fake-name/EORE/Code/Prototypes/SWR Sweeper/takeSweeps.py

import time

import eore
import SignalHound as sh
import logSetup



ACQ_SPAN               = 27e6
ACQ_REF_LEVEL_DB       = -20
ACQ_ATTENUATION_DB     = 20
ACQ_GAIN_SETTING       = 0
ACQ_RBW                = 2.465e3
ACQ_VBW                = ACQ_RBW
ACQ_SWEEP_TIME_SECONDS = 0.0100
ACQ_WINDOW_TYPE        = "hamming"
ACQ_UNITS              = "power"
ACQ_TYPE               = "sweeping"
ACQ_MODE               = "average"
ACQ_Y_SCALE            = "log-scale"

# The offset from center to locate the sampling bin at.
SAMPLE_OFFSET          = 5e6

class SweeperSignalHound(sh.SignalHound):


	def setupSignalhound(self, freq=100e6):
		self.configureAcquisition(ACQ_MODE, ACQ_Y_SCALE)
		self.configureCenterSpan(center = freq+5e6, span = ACQ_SPAN)
		self.configureLevel(ref = ACQ_REF_LEVEL_DB, atten = ACQ_ATTENUATION_DB)
		self.configureGain(gain = ACQ_GAIN_SETTING)
		self.configureSweepCoupling(rbw = ACQ_RBW, vbw = ACQ_VBW, sweepTime = ACQ_SWEEP_TIME_SECONDS, rbwType = "native", rejection = "no-spur-reject")
		self.configureWindow(window = ACQ_WINDOW_TYPE)
		self.configureProcUnits(units = ACQ_UNITS)
		self.configureTrigger(trigType = "none", edge = "rising-edge", level = 0, timeout = 5)
		# self.configureIO("dc", "int-ref-out", "out-logic-low")
		# self.configureDemod("fm", 102.3e6, 250e3, 12e3, 20, 50)

		# self.configureRawSweep(100, 8, 2)
		self.initiate(mode = ACQ_TYPE, flag = "ignored")
		print(self.getCurrentAcquisitionSettings())

	def setAcqCenterFreq(self, freq):
		self.configureCenterSpan(center = freq, span = ACQ_SPAN)
		self.initiate(mode = ACQ_TYPE, flag = "ignored")

	def getPowerAtFreq(self, freq):

		self.setAcqCenterFreq(freq-SAMPLE_OFFSET)

		trace = self.fetchTrace()
		traceSize = len(trace['max'])
		# Binsize is span divided by number of returned points
		acqBinSize = ACQ_SPAN / traceSize

		# the offset of the frequency we're interested in is
		binFreqOffset = int(SAMPLE_OFFSET / acqBinSize)

		binFreqCenter = (traceSize / 2) + binFreqOffset

		# Return the max of the three frequency bins around the point of interest
		ret = max(trace['max'][binFreqCenter-3:binFreqCenter+4])

		# print(traceSize, trace['max'].argmax(), binFreqCenter)
		print(ret, max(trace['max']))
		# print(trace['max'][binFreqCenter-1:binFreqCenter+4])

		return ret

def frange(x, y, jump):
	while x <= y:
		yield x
		x += jump


# import matplotlib
# matplotlib.use("WxAgg")		#Change ploting backend

import matplotlib.pyplot as pplt
import numpy as np

def plot(dataset):
	mainWin = pplt.figure()

	plot1 = mainWin.add_subplot(1,1,1)			#And plot them

	x = []
	y = []
	for xVal, yVal in dataset:
		if y < -60:
			continue
		if x < -60:
			continue

		x.append(xVal)
		y.append(yVal)

	plot1.plot(x, y)

	pplt.show()

def go():
	print("Starting")
	# logSetup.initLogging()
	print("Loggers initialized")
	# port = EoreController("COM4")
	port = eore.EoreController("COM40")
	print("Port opened")

	x = 0
	port.writeAtten(eore.MAIN_TONE_ATTEN,       20)
	port.writeAtten(eore.SWITCH_SWR_TONE_ATTEN, 10)
	port.writeAtten(eore.NOISE_DIODE_ATTEN,     0)
	port.writeAtten(eore.AUX_TONE_ATTEN,        0)
	port.writeAtten(eore.SWITCH_TONE_ATTEN,     0)
	port.writeAtten(eore.MID_AMP_ATTEN,         10)


	port.writeSwitch(eore.MAIN_SW, eore.SW_MAIN_INPUT)
	port.writeSwitch(eore.TONE_SW, eore.SW_TONE_SWR_COUPLER)

	# port.writeAtten(2, 31.5)

	port.writeOscillator(0, 100e6)

	START = 100e6
	STOP  = 200e6

	# START = 195.0e6
	# STOP  = 200.0e6
	STEP  = 2.5e5


	# while (1):
	# return

	hound = SweeperSignalHound()
	print("SignalHound connected")
	hound.setupSignalhound()
	print("SignalHound configured")


	data = []

	with open("log - %s.csv" % time.time(), "w") as fp:

		fp.write("# Start: %s\n" % START)
		fp.write("# Stop:  %s\n" % STOP)
		fp.write("# Step:  %s\n" % STEP)

		for x in frange(START, STOP, STEP):
			print("LOOPIN")
			ret = port.writeOscillator(0, x)
			time.sleep(0.050)
			# print(x, ret)
			trace = hound.getPowerAtFreq(x)
			# print(ret)
			print(x, trace)
			fp.write("%s, %s\n" % (x, trace))

			data.append((x, trace))

	plot(data)


if __name__ == "__main__":
	go()
